eltortugo/audioxtreamer/VHDL/usb2iis/cy16_to_fifo.vhd

 library IEEE;
use IEEE.STD_LOGIC_1164.ALL;

-- Uncomment the following library declaration if using
-- arithmetic functions with Signed or Unsigned values
use IEEE.NUMERIC_STD.ALL;
use ieee.std_logic_unsigned.all;

-- Uncomment the following library declaration if instantiating
-- any Xilinx leaf cells in this code.
library UNISIM;
use UNISIM.VComponents.all;


use work.common_types.all;
------------------------------------------------------------------------------------------------------------
------------------------------------------------------------------------------------------------------------
entity cy16_to_fifo is
generic(
  max_sdo_lines: positive := 32
);
  Port (
    --usb interface
    usb_clk : in STD_LOGIC;
    reset : in STD_LOGIC;
    -- DATA IO

    usb_data : in slv_16;
    -- FIFO control
    usb_oe  : in std_logic; --signals a read grant
    usb_empty : in  STD_LOGIC;
    usb_rd_req : out STD_LOGIC; --signals a read request

    nr_outputs : in std_logic_vector(3 downto 0);

    out_fifo_full : in std_logic;
    out_fifo_wr   : out std_logic;
    out_fifo_data : out slv24_array(0 to (max_sdo_lines*2)-1);

    midi_out_wr   : out slv_8;
    midi_out_data : out slv8_array ( 0 to 7 )
    );
end cy16_to_fifo;
------------------------------------------------------------------------------------------------------------
------------------------------------------------------------------------------------------------------------

architecture rtl of cy16_to_fifo is

signal rd_data : std_logic_vector(15 downto 0);

signal rd_req :std_logic;
signal stall_rd :std_logic;

signal rvalid   : std_logic;
signal reg_oe  : std_logic;

-- RX FSM
type rx_state_t is ( cmd, w0, w1, w2, midi);
signal rx_state : rx_state_t;
--attribute fsm_encoding : string;
--attribute fsm_encoding of rx_state : signal is "one-hot";

-- packet decoding

signal cmd_reg : slv_16;
signal audio_valid: std_logic;

signal midi_valid: std_logic;
signal midi_done : std_logic;
signal midi_sizes: slv_16;

signal outs_counter, active_outs: natural range 0 to max_sdo_lines;

-- out_fifo signals

signal out_fifo_data_regs : slv24_array(0 to (max_sdo_lines*2)-1);
signal midi_index : natural range 0 to 12;

attribute keep : string;
attribute keep of midi_valid : signal is "true";
attribute keep of audio_valid : signal is "true";

------------------------------------------------------------------------------------------------------------
------------------------------------------------------------------------------------------------------------
begin

------------------------------------------------------------------------------------------------------------
register_inputs : process (usb_clk)
begin
  if rising_edge(usb_clk) then
    if reset = '1' then
      rd_data <= X"CDCD";
    else
      rd_data <= usb_data;
    end if;
  end if;
end process;
------------------------------------------------------------------------------------------------------------
rvalid_reg : process (usb_clk)
begin
  if rising_edge(usb_clk) then
    if reset = '1' then
      rvalid <= '0';
    elsif usb_empty = '0' and rd_req = '0' and usb_oe = '1' then 
      rvalid <= '1';
    else
      rvalid <= '0';
    end if;
  end if;
end process;
------------------------------------------------------------------------------------------------------------
read_reg : process (usb_clk)
begin
  if rising_edge(usb_clk) then
    reg_oe <= usb_oe;
    if reset = '1'
     or (outs_counter = active_outs-1 and out_fifo_full = '1') then
      stall_rd <= '1';
    elsif rd_req = '1' and out_fifo_full = '0' and usb_oe = '1' and reg_oe = '0' then
      stall_rd <= '0';
    end if;
  end if;
end process;
------------------------------------------------------------------------------------------------------------
rd_req <= '1' when (outs_counter = active_outs-1 and rx_state = w2 and stall_rd = '1') else '0';
usb_rd_req <= rd_req;
------------------------------------------------------------------------------------------------------------
rcvr_FSM: process (usb_clk)
begin
  if rising_edge(usb_clk) then
    if reset = '1' then
      rx_state <= cmd;
    else  
      case rx_state is
      when cmd =>
        if rvalid = '1' and active_outs /= 0 then
          if audio_valid = '1' then
            rx_state <= w0;
          elsif midi_valid = '1' then
            rx_state <= midi;
          end if;
        end if;
      when w0 =>
        if rvalid = '1' then
          rx_state <= w1;
        end if;
      when w1 =>
        if rvalid = '1' then
          rx_state <= w2;
        end if;
      when w2 =>
        if outs_counter < active_outs-1  then
          if rvalid = '1' then
            rx_state <= w0;
          end if;
        else
          if out_fifo_full = '0' and (rvalid = '1' or (stall_rd = '1' and usb_oe = '1' and reg_oe = '0')) then --only if we manage to write, otherwise wait here
            rx_state <= cmd;
          end if;
        end if;

      when midi =>
        if midi_done = '1' then 
          rx_state <= cmd;
        end if;
      end case;

    end if;
  end if; 
end process;

------------------------------------------------------------------------------------------------------------
audio_valid <= '1' when rx_state = cmd and cmd_reg = X"55AA" and rd_data = X"AA55" else '0';
------------------------------------------------------------------------------------------------------------
midi_valid  <= '1' when rx_state = cmd and cmd_reg = X"6996" and rd_data = X"9669" else '0';
------------------------------------------------------------------------------------------------------------
process (usb_clk)
begin
  if rising_edge(usb_clk) then
    if reset = '1' then
      cmd_reg <= X"0000";
    elsif rx_state = cmd then
      if rvalid = '1' then
        if audio_valid = '0' and midi_valid = '0' then
          cmd_reg <= rd_data;
        else
          cmd_reg <= X"0000" ; -- invalidate the header
        end if;
      end if;
    end if; 
  end if;
end process;

------------------------------------------------------------------------------------------------------------
active_outs <= to_integer(unsigned(nr_outputs)) + 1 ;
------------------------------------------------------------------------------------------------------------
process (usb_clk)
begin
  if rising_edge (usb_clk) then
    if reset = '1' or audio_valid = '1' then
      outs_counter <= 0;
    elsif rx_state = w2 and rvalid = '1' and outs_counter < active_outs-1 then
      outs_counter <= outs_counter+1;
    end if;
  end if;
end process;

------------------------------------------------------------------------------------------------------------
out_fifo_wr <= '1' when 
  rx_state = w2 and
  (rvalid = '1' or (stall_rd = '1' and usb_oe = '1' and reg_oe = '0'))and
  outs_counter = active_outs-1 and
  out_fifo_full = '0'
  else '0';
------------------------------------------------------------------------------------------------------------
rx_fifos : for i in 0 to max_sdo_lines-1 generate

  process (usb_clk)
  begin
    if rising_edge(usb_clk) then
      if reset = '1' then
        out_fifo_data_regs(i*2)     <= (others => '0');
        out_fifo_data_regs((i*2)+1) <= (others => '0');
      elsif i = outs_counter and rvalid = '1' then
        case rx_state is
        when w0 => out_fifo_data_regs(i*2)(15 downto 0) <= rd_data;
        when w1 => out_fifo_data_regs(i*2)(23 downto 16) <= rd_data(7 downto 0);
                        out_fifo_data_regs((i*2)+1)(7 downto 0) <= rd_data(15 downto 8);
        when w2 => out_fifo_data_regs((i*2)+1)(23 downto 8) <= rd_data;
        when others =>
        end case;
      end if;
    end if;
  end process;
  out_fifo_data(i*2) <= out_fifo_data_regs(i*2);--right channels
  out_fifo_data((i*2)+1) <= out_fifo_data_regs((i*2)+1);

end generate;

midi_done <= '1' when midi_index = 12 else '0';

p_midi_out :process (usb_clk)
begin
  if rising_edge(usb_clk) then

    if rx_state = midi and midi_index < 12 then 
      midi_index <= midi_index + 1;
    else
      midi_index <= 0;
    end if;


    midi_out_wr <= (others => '0');

    if rx_state = midi then
      if midi_index = 0 then
        midi_sizes <= rd_data;
      else

        for i in 0 to 3 loop

          midi_out_data(i*2) <= rd_data(7 downto 0);
          midi_out_data(i*2+1) <= rd_data(15 downto 8);

          if midi_index = i+1 then
            if midi_sizes(i*4+1 downto i*4) > 0 then
              midi_out_wr(i*2) <= '1';
            end if;
            if midi_sizes(i*4+3 downto i*4+2) > 0 then
              midi_out_wr(i*2+1) <= '1';
            end if;
          end if;

          if midi_index = i+5 then
            if midi_sizes(i*4+1 downto i*4) > 1 then
              midi_out_wr(i*2) <= '1';
            end if;
            if midi_sizes(i*4+3 downto i*4+2) > 1 then
              midi_out_wr(i*2+1) <= '1';
            end if;
          end if;

          if midi_index = i+9 then
            if midi_sizes(i*4+1 downto i*4) > 2 then
              midi_out_wr(i*2) <= '1';
            end if;
            if midi_sizes(i*4+3 downto i*4+2) > 2 then
              midi_out_wr(i*2+1) <= '1';
            end if;
          end if;
        end loop;
      end if;
    end if;
  end if;
end process;

end rtl;
